remidavidkoster/Redako-PDNAnalyzer/Simulations/PDN Analyzer Current Drive.asc

C2: cap; {C}
C3: cap; 0.5p
C4: cap; 0.5p
C5: cap; {C}
C6: cap; {C}
DUT: res; {R}
L2: ind; 2n
L3: ind; 10n
L4: ind; 10n
L5: ind; 2n
L6: ind; 2n
L7: ind; 10n
L8: ind; 10n
LShunt: ind; 1n
R2: EuropeanResistor; 50m
R3: EuropeanResistor; 1k
R4: EuropeanResistor; 1k
R5: EuropeanResistor; 10k
R6: EuropeanResistor; 10k
R7: EuropeanResistor; 10m
R8: EuropeanResistor; 10m
R9: EuropeanResistor; 100
R10: EuropeanResistor; 100
R11: EuropeanResistor; 10k
R12: EuropeanResistor; 10k
R13: EuropeanResistor; 200k
R14: EuropeanResistor; 200k
R15: EuropeanResistor; 100
R16: EuropeanResistor; 100
R17: EuropeanResistor; 1k
R18: EuropeanResistor; 1k
R19: EuropeanResistor; 50m
R21: EuropeanResistor; 50m
R22: EuropeanResistor; 10m
R23: EuropeanResistor; 10m
R24: EuropeanResistor; 200k
R25: EuropeanResistor; 200k
Shunt: EuropeanResistor; 0.5
U1: OPA891
U3: ADA4940
U6: ADA4940
V1: voltage; 2.5
V2: voltage; 2.5
V3: voltage; 3.3
V4: voltage; 5
V5: voltage; 5
V6: signal; SINE(0 0.1 1K); AC 0.1
Named nets: +5V, -5V, Dut+, Dut-, +2.5V, -2.5V, 0, 1+, 1-, 2+, 2-, W1
.ac dec 100 1 25Meg
.param C=1000M
Shunt
DC Bias Cap
Wiring
Wiring
DC Bias Caps
AD2
.param R 1m
